MaxMaximilian/Synology-NAS-DIY-USV-UPS/images/Label.JPG

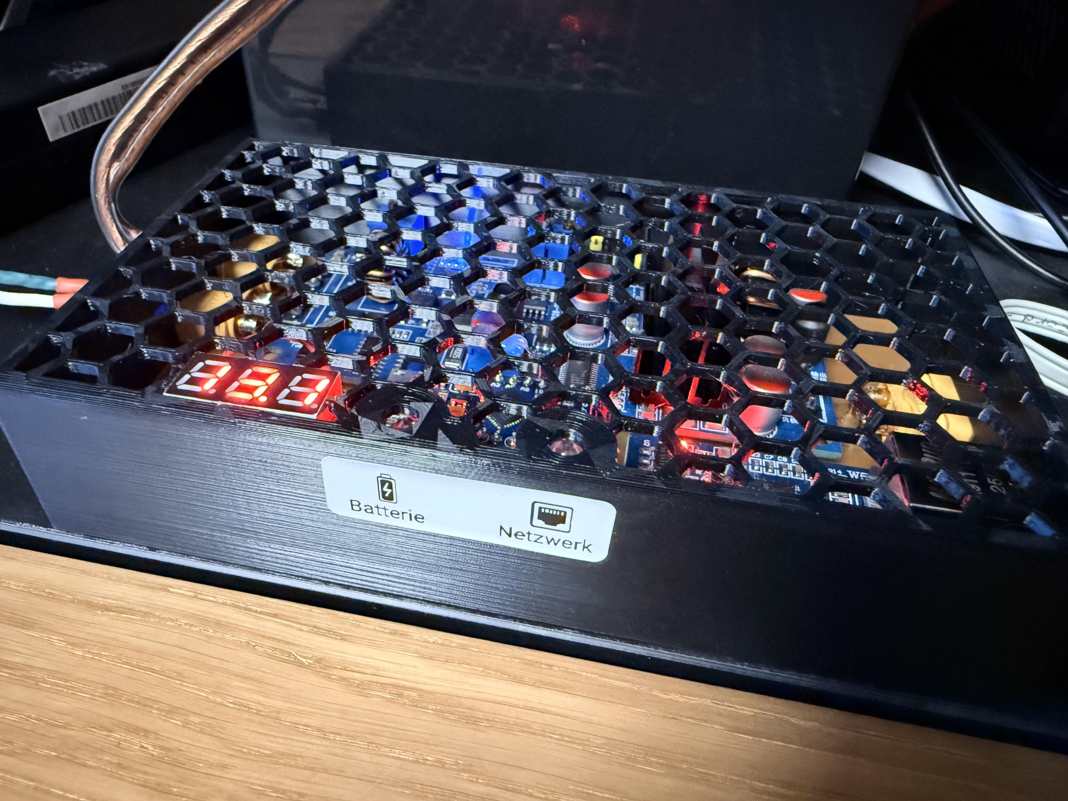
images/Label.JPG
