MaxMaximilian/Synology-NAS-DIY-USV-UPS/images/PCB.JPG

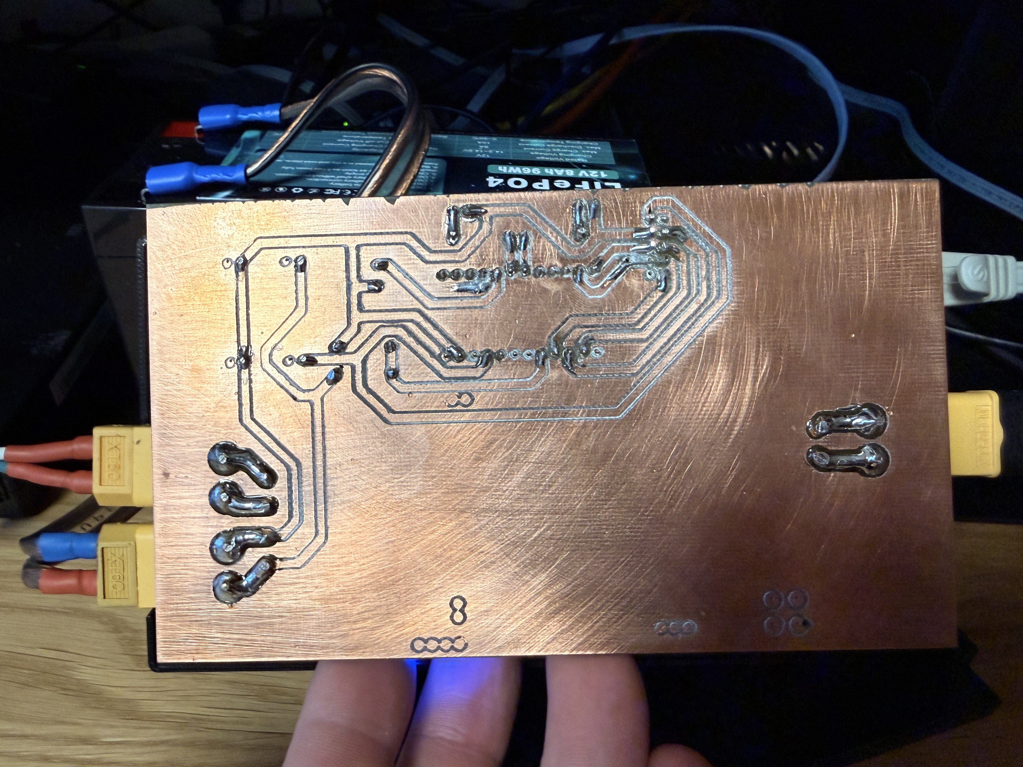
images/PCB.JPG
