MaxMaximilian/Synology-NAS-DIY-USV-UPS/software/python/1 Scedule General.jpg

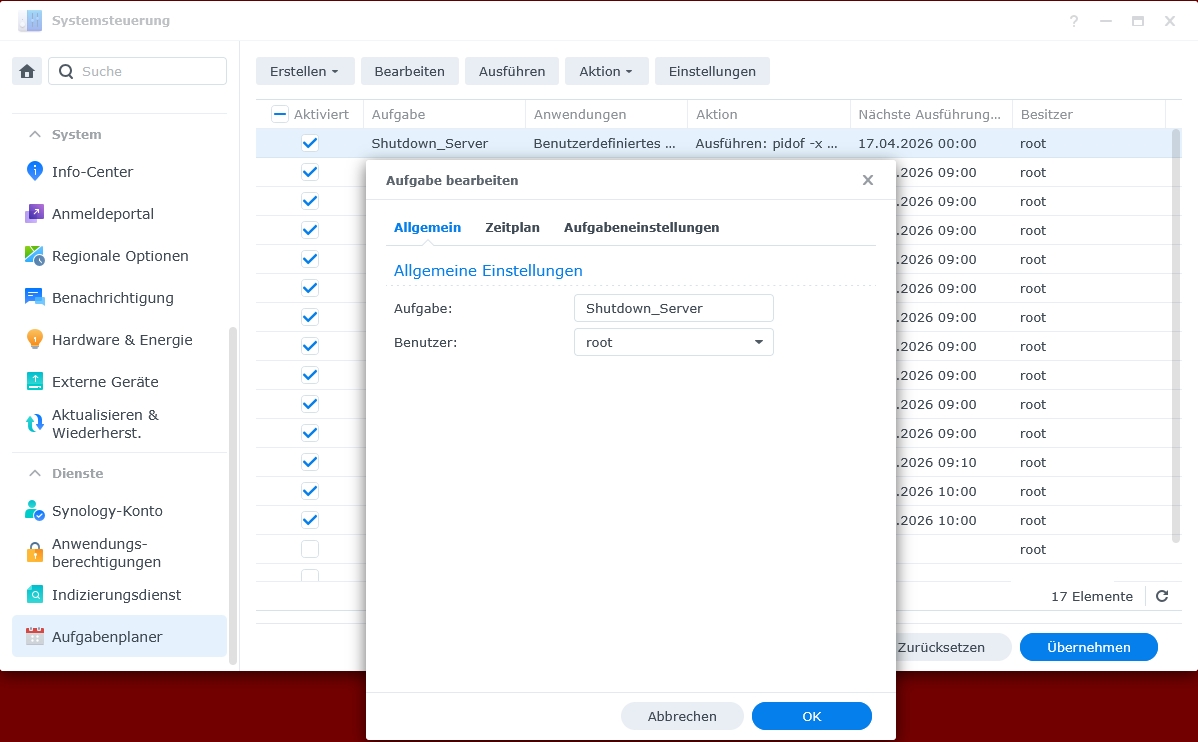
software/python/1 Scedule General.jpg
