MaxMaximilian/Synology-NAS-DIY-USV-UPS/software/python/2 Scedule Timing.jpg

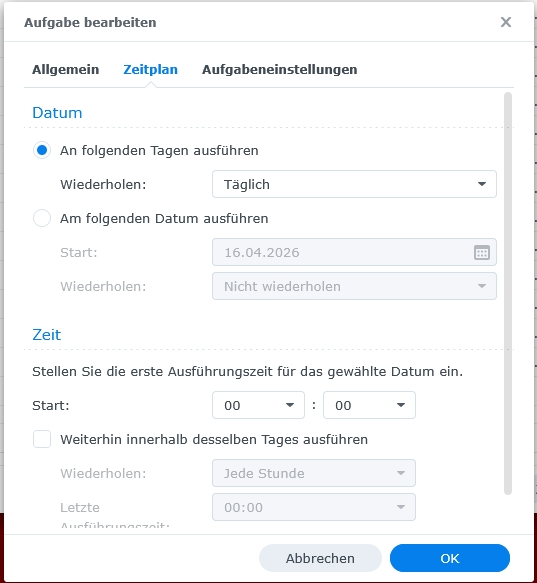
software/python/2 Scedule Timing.jpg
