MaxMaximilian/Synology-NAS-DIY-USV-UPS/software/python/3 Scedule Script.jpg

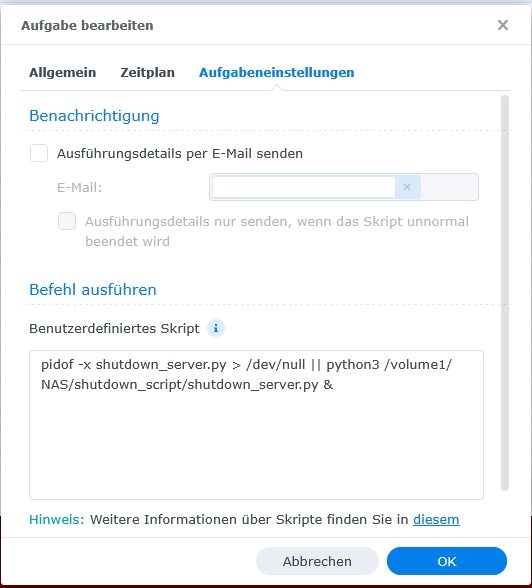
software/python/3 Scedule Script.jpg
